fabriziotappero/softmic/tmp/ESP32-example.jpg

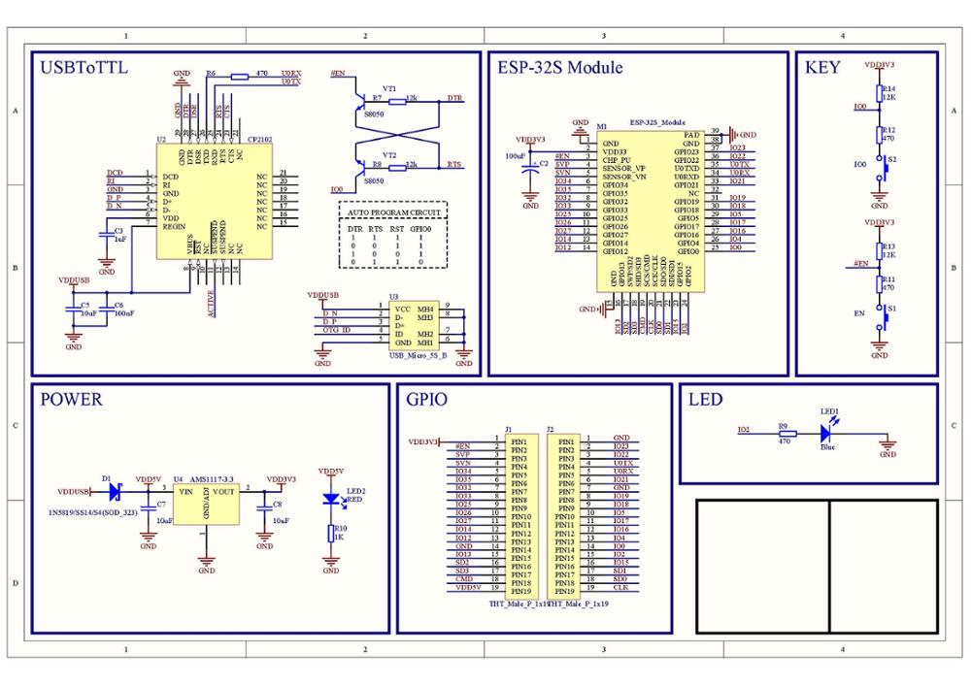
tmp/ESP32-example.jpg
