fabriziotappero/softmic/sim/softmic-sim.asc

C1: cap; 22p
C2: cap; 1µ
C3: cap; 1µ
C4: cap; 47µ
C5: cap; 200µ
C6: cap; 1n
C7: cap; 1n
C8: cap; 5n
C9: cap; 5n
C10: cap; 1µ
C11: cap; 1µ
D1: zener; 1N750
Q1: npn; 2N2369
R1: res; 1000k
R2: res; 2k
R3: res; 11k
R4: res; 450
R5: res; 340
R6: res; 47
R7: res; 47
R8: res; 100k
R9: res; 200k
R10: res; 180k
R11: res; 100k
R12: res; 12k
R13: res; 18k
R14: res; 1k
R15: res; 11k
R16: res; 200k
R17: res; 170k
R18: res; 1
R19: res; 420k
R20: res; 1k
R21: res; 11k
U1: njf; LSK170A
U2: OPA1671
U3: OPA1671
V1: voltage; SINE(0 20m 2k); AC 1 1k
V2: battery; 5
Named nets: 0, JFET-OUT, VCC, OUT1, V1-OUT, OUT2
.tran 0 10m 0 100u
Voltage gain: 9dB
600uA
Voltage gain: 23dB
ADC MAX11613
4.7V
MIC-IN1
XLR-1
XLR-2
XLR-3
POWER SUPPLY
BALANCED XLR OUTPUT
5V-IN
ESP32-WROOM-32E
I2C-1
MIC-IN2
Line Out Level = +4dBu = 1.78dBV = 1.23VRMS = 3.47Vpp
Typical Mic gain = 0
Typical Mic Level = -30dBu to -60dBu = 24.50mVRMS to 0.77mVRMS
14mVRMS
Audio Pre Amplifier, 32dB gain, 20Hz to 20kHz at -1dB bandwidth
TYPICAL VALUES FOR PROFESSIONAL AUDIO DEVICES
Voltage gain: 23dB
Typical Pre-Amp Gain = 40dB to 60dB
VppMAX=180mV
Vref=2V
3V3
3V3
@ Fabrizio Tappero, all rights reserved
